RenayaAjiAydinaHazela/SunSense/Desain 3D/IMG-20250427-WA0000.jpg

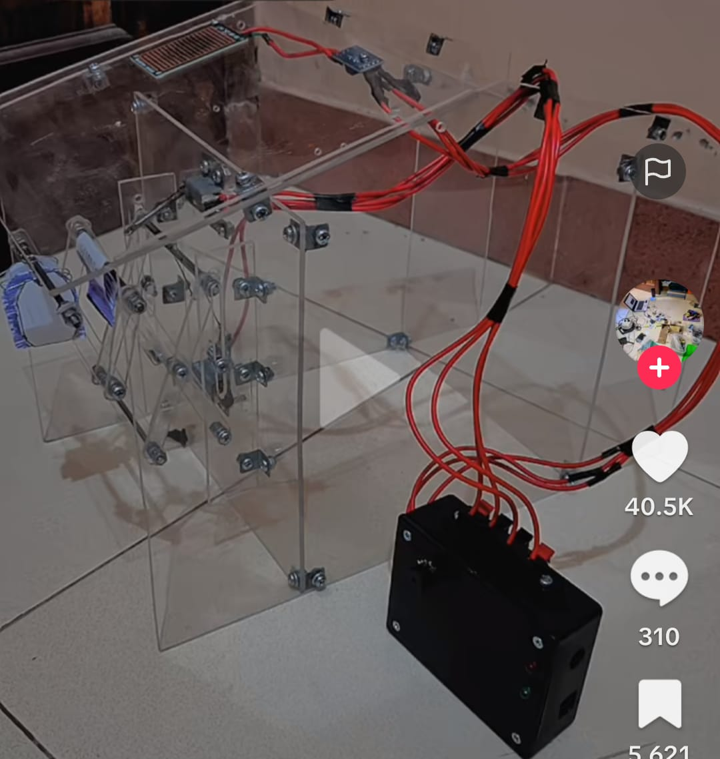
Desain 3D/IMG-20250427-WA0000.jpg
