RenayaAjiAydinaHazela/SunSense/Desain 3D/IMG-20250505-WA0067.jpg

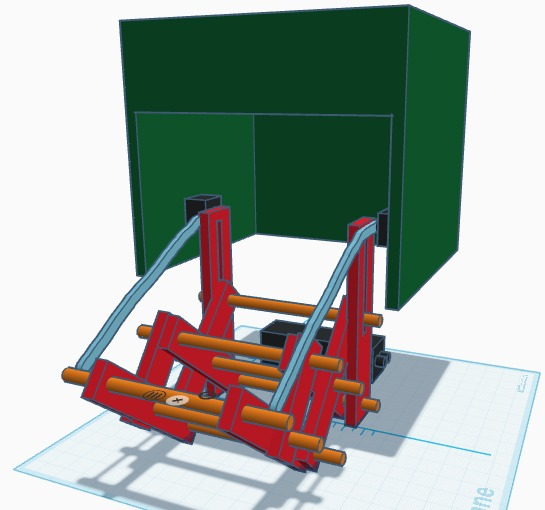
Desain 3D/IMG-20250505-WA0067.jpg
