RenayaAjiAydinaHazela/SunSense/Desain 3D/IMG-20250505-WA0068.jpg

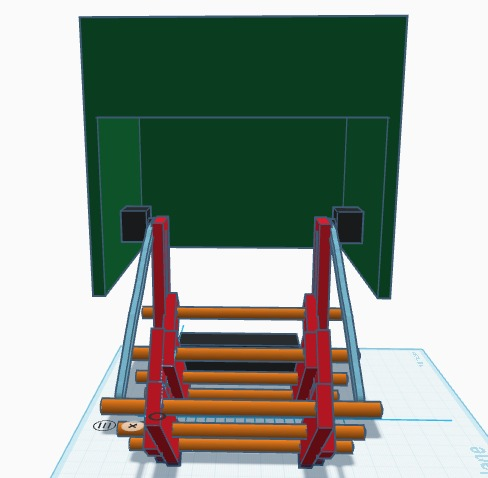
Desain 3D/IMG-20250505-WA0068.jpg
