RenayaAjiAydinaHazela/SunSense/Desain 3D/IMG-20250505-WA0069.jpg

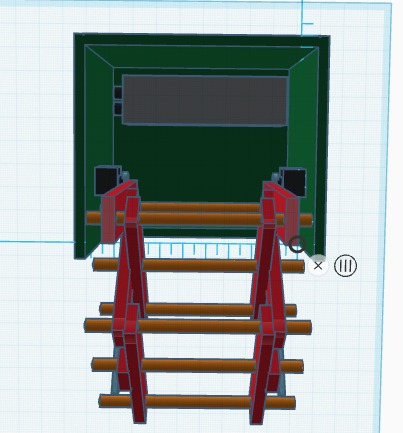
Desain 3D/IMG-20250505-WA0069.jpg
