RenayaAjiAydinaHazela/SunSense/Desain 3D/Screenshot_2025-04-29-11-31-40-04_99c04817c0de5652397fc8b56c3b3817.jpg

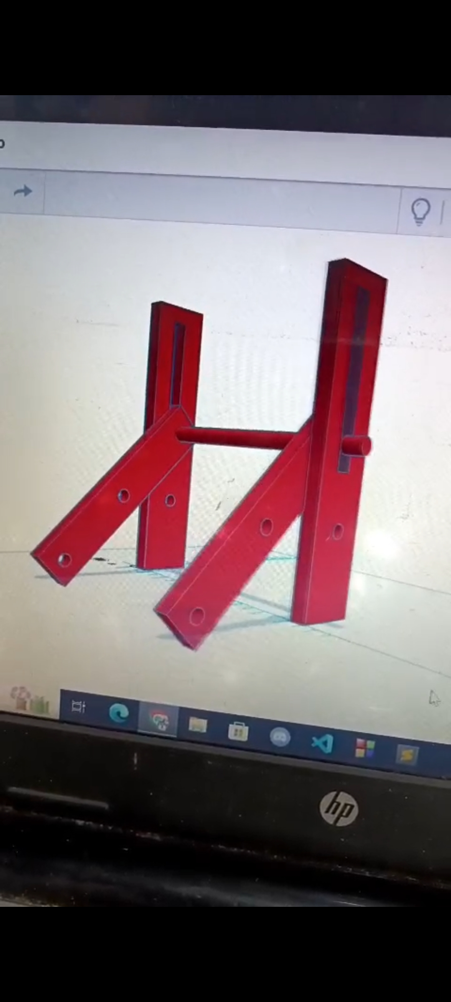
Desain 3D/Screenshot_2025-04-29-11-31-40-04_99c04817c0de5652397fc8b56c3b3817.jpg
