RenayaAjiAydinaHazela/SunSense/Desain UI UX/Figma_GRAFIK_NEW.jpg

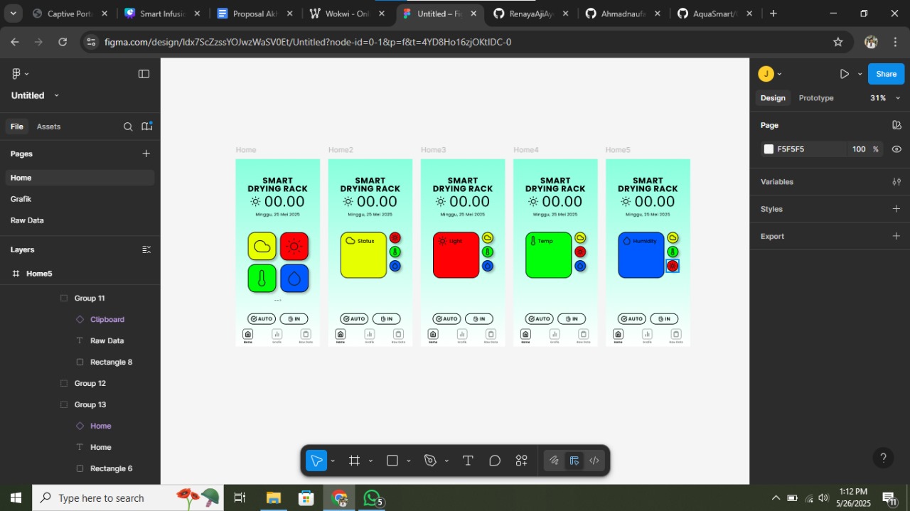
Desain UI UX/Figma_GRAFIK_NEW.jpg
