RenayaAjiAydinaHazela/SunSense/Desain UI UX/Figma_HOME.jpg

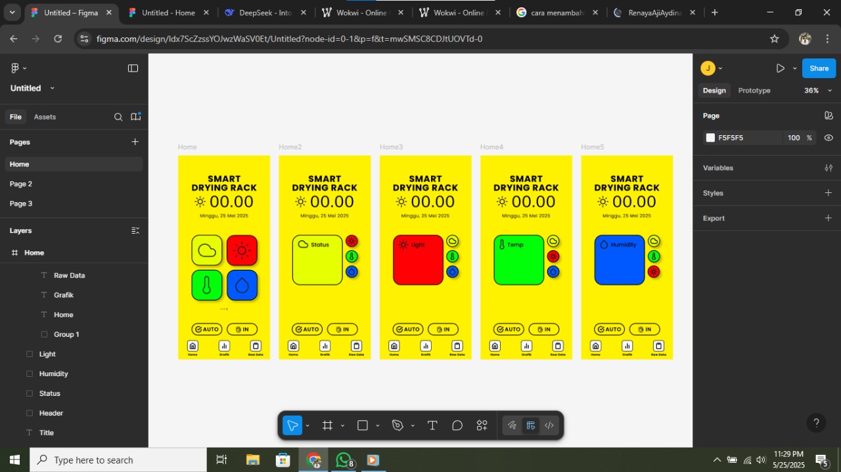
Desain UI UX/Figma_HOME.jpg
