RenayaAjiAydinaHazela/SunSense/Desain UI UX/Figma_HOME_NEW.jpg

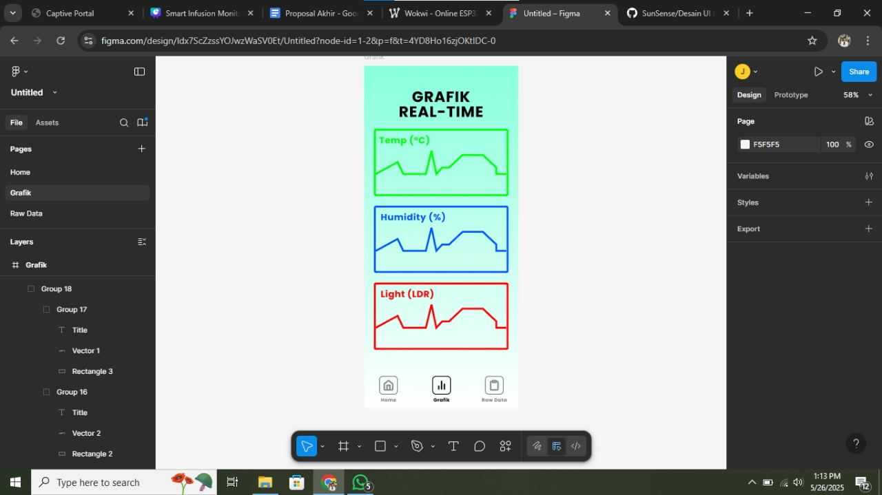
Desain UI UX/Figma_HOME_NEW.jpg
