RenayaAjiAydinaHazela/SunSense/Desain UI UX/Figma_RAW DATA_NEW.jpg

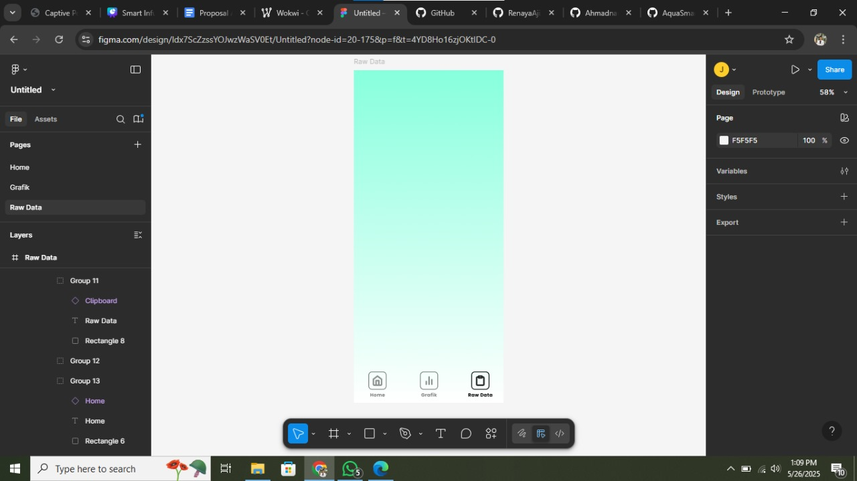
Desain UI UX/Figma_RAW DATA_NEW.jpg
