RenayaAjiAydinaHazela/SunSense/Program/Asset/GUI1.jpg

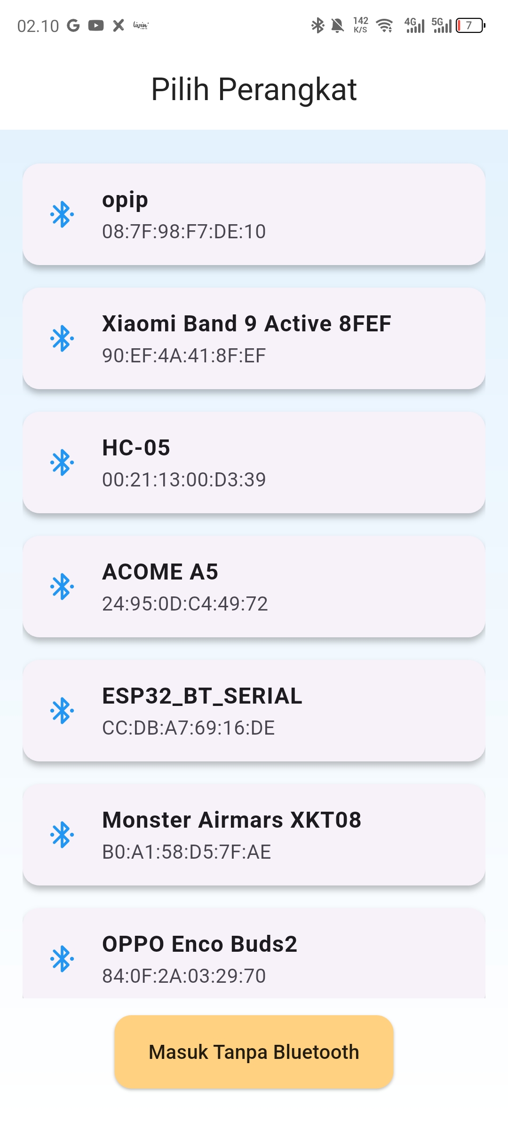
Program/Asset/GUI1.jpg
