RenayaAjiAydinaHazela/SunSense/Program/Asset/GUI2.jpg

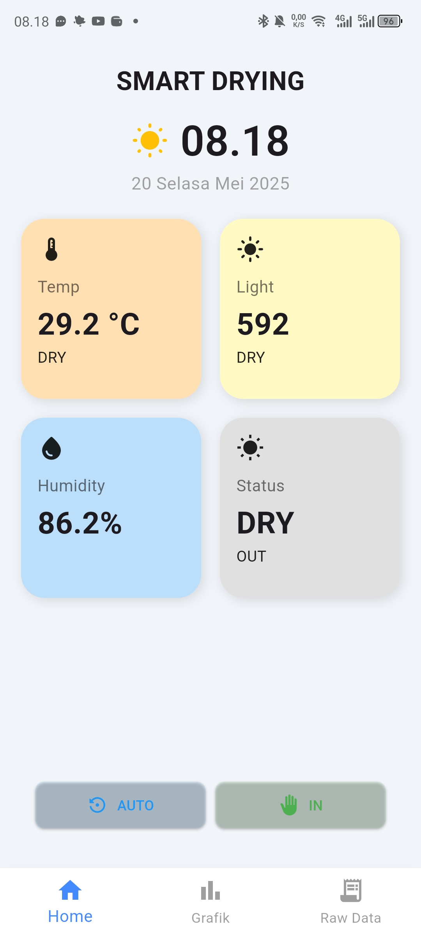
Program/Asset/GUI2.jpg
