RenayaAjiAydinaHazela/SunSense/Program/Asset/GUI3.jpg

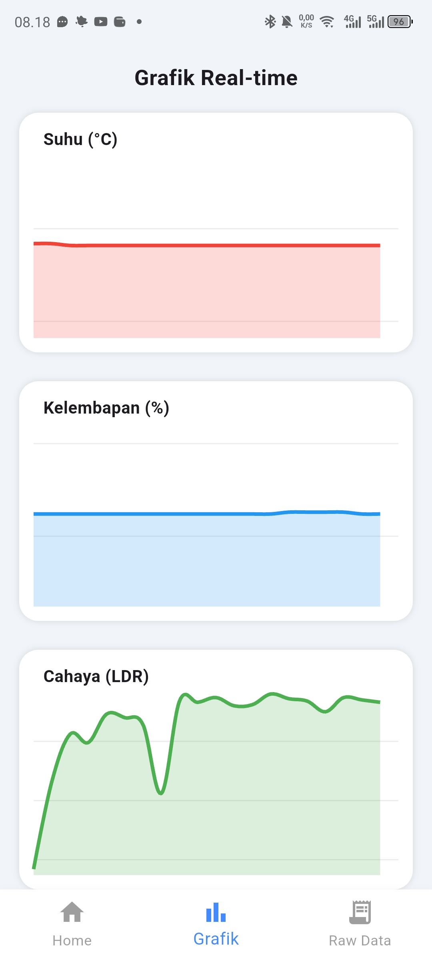
Program/Asset/GUI3.jpg
