RenayaAjiAydinaHazela/SunSense/Program/Asset/GUI4.jpg

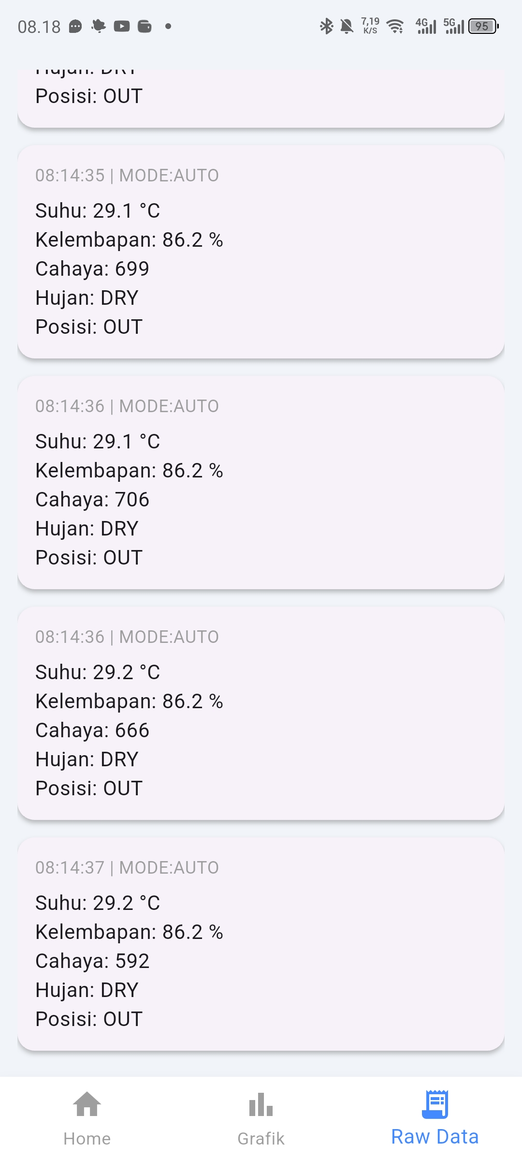
Program/Asset/GUI4.jpg
