RenayaAjiAydinaHazela/SunSense/Program/Asset/Screenshot 2025-05-12 014103.png

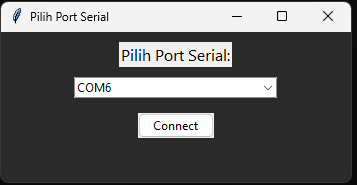
Program/Asset/Screenshot 2025-05-12 014103.png
