RenayaAjiAydinaHazela/SunSense/Program/Asset/Screenshot 2025-05-12 014132.png

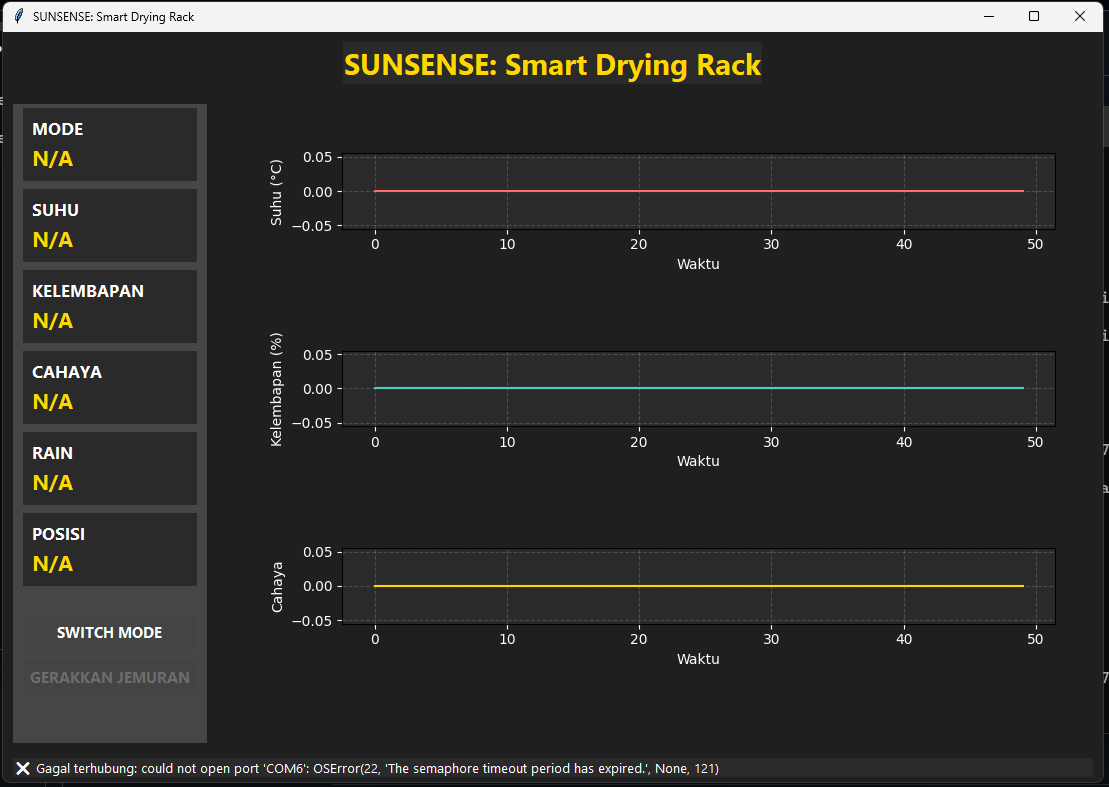
Program/Asset/Screenshot 2025-05-12 014132.png
